alfred-wrigfors/1DT305/firmware/include/constants.hpp

#ifndef CONSTANTS_HPP
#define CONSTANTS_HPP

// WiFi
const char* SSID     = "12345678";
const char* PASSWORD = "12345678";

const char* SERVER      = "xxx.xxx.x.xx";
const int   PORT        = 5000;
const char* ENDPOINT    = "api/put";

const float TEMP_COEFF  = -0.3158845;
const float TEMP_OFFSET =  590.3520278;

const int   RETRIES     = 5;

const float BAT_COEFF   = 3.20;
const float BAT_MIN     = 7.2;
const float BAT_MAX     = 9.6;


#endif
